st7712/nexo/hardware/CAD/PSU holder.stl

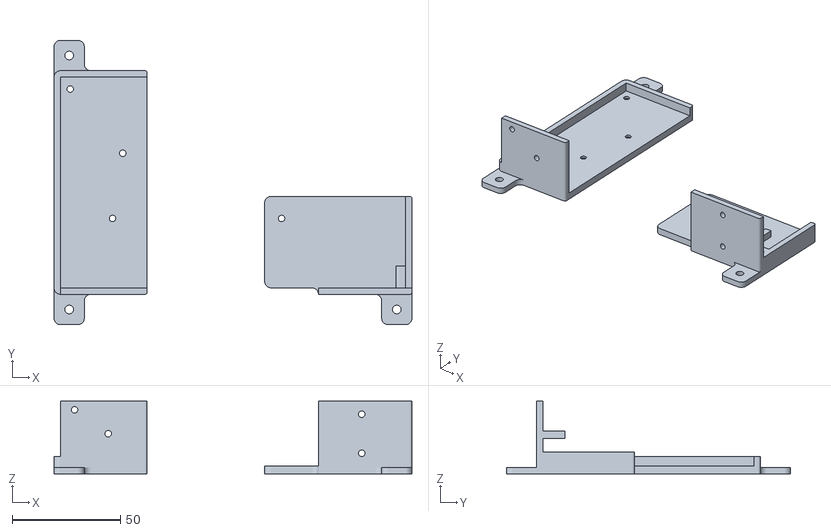
[picture p15: CAD file, 2026-02-17]
hardware/CAD/PSU holder.stl
165.2 x 131.2 x 33.5
