st7712/nexo/hardware/CAD/wood curve jig 1.stl

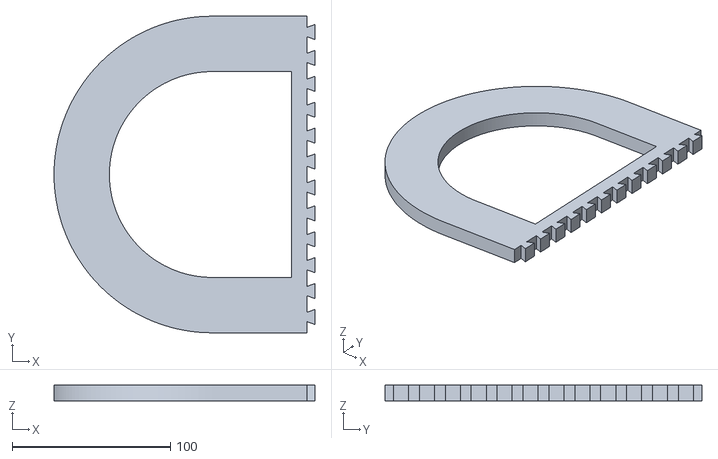
[picture p16: CAD file, 2026-02-17]
hardware/CAD/wood curve jig 1.stl
164.8 x 200.0 x 10.0
