st7712/nexo/hardware/CAD/speaker bottom rubber v3.stl

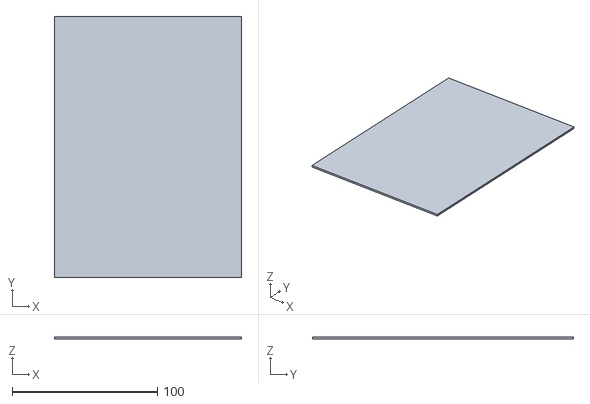
[picture p17: CAD file, 2026-02-17]
hardware/CAD/speaker bottom rubber v3.stl
129.0 x 180.0 x 1.50
