st7712/nexo/hardware/CAD/inside plaster enclosure 1.stl

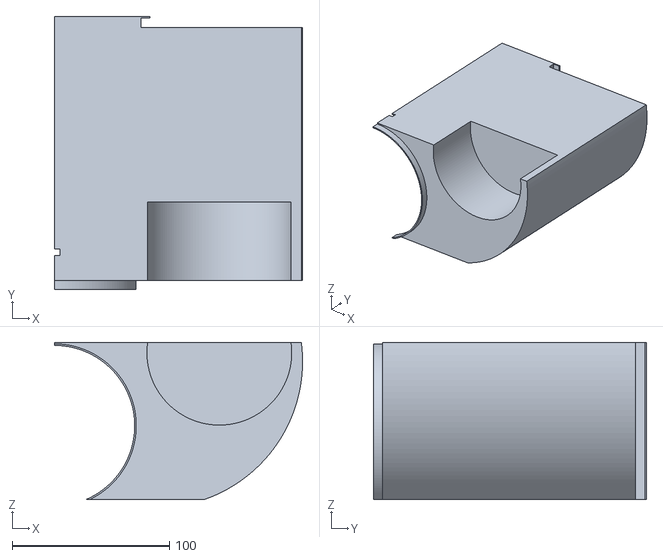
[picture p18: CAD file, 2026-02-17]
hardware/CAD/inside plaster enclosure 1.stl
158.0 x 173.8 x 100.2
