st7712/nexo/hardware/CAD/inside plaster enclosure 2.stl

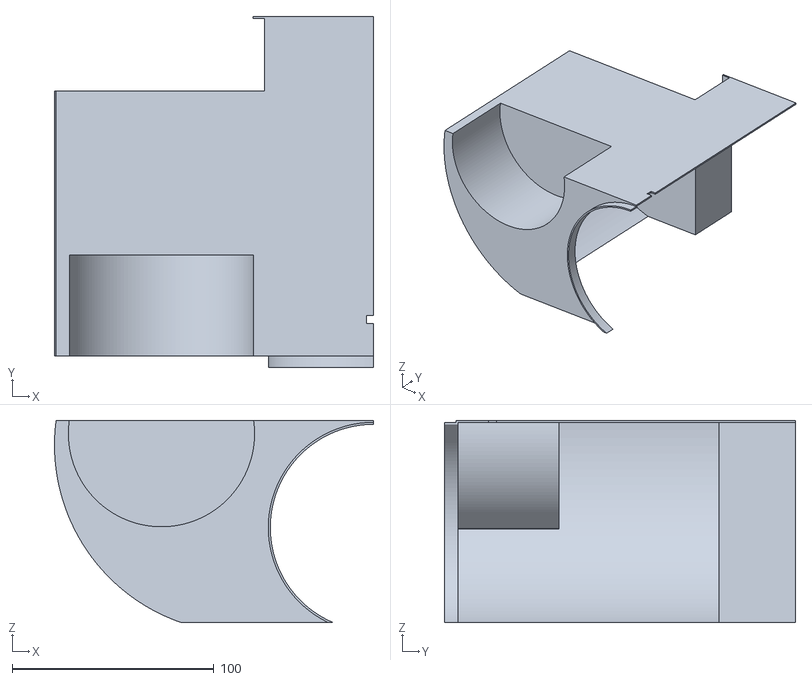
[picture p19: CAD file, 2026-02-17]
hardware/CAD/inside plaster enclosure 2.stl
158.0 x 173.8 x 100.2
