st7712/nexo/hardware/CAD/inside plaster enclosure top.stl

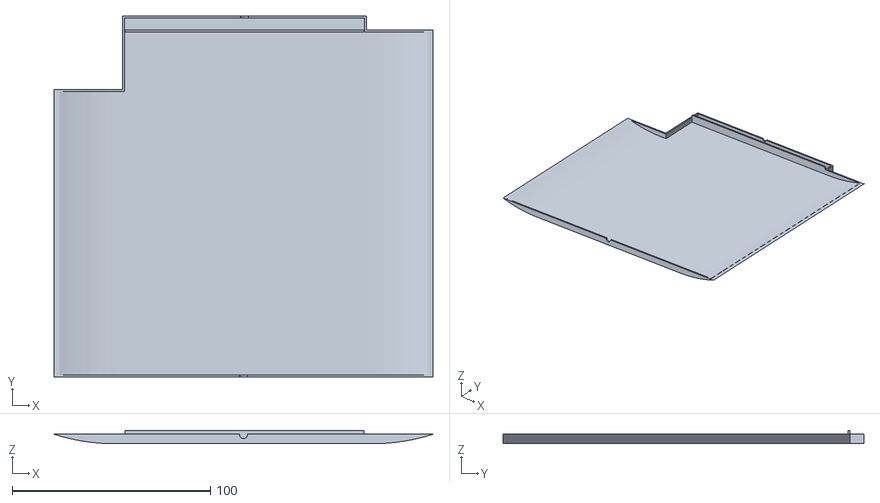
[picture p20: CAD file, 2026-02-17]
hardware/CAD/inside plaster enclosure top.stl
191.2 x 182.0 x 6.80
