st7712/nexo/hardware/CAD/front plate 1.stl

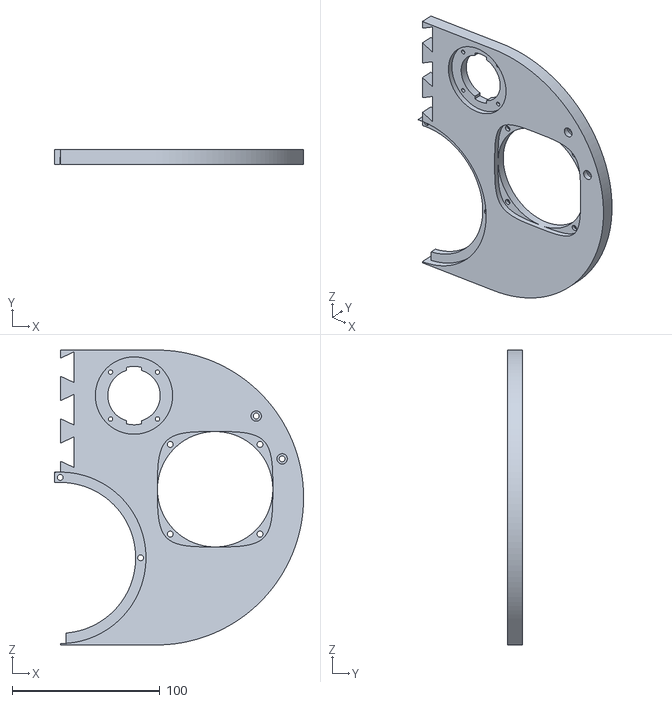
[picture p21: CAD file, 2026-02-17]
hardware/CAD/front plate 1.stl
169.0 x 10.0 x 200.0
