st7712/nexo/hardware/CAD/back plate 1.stl

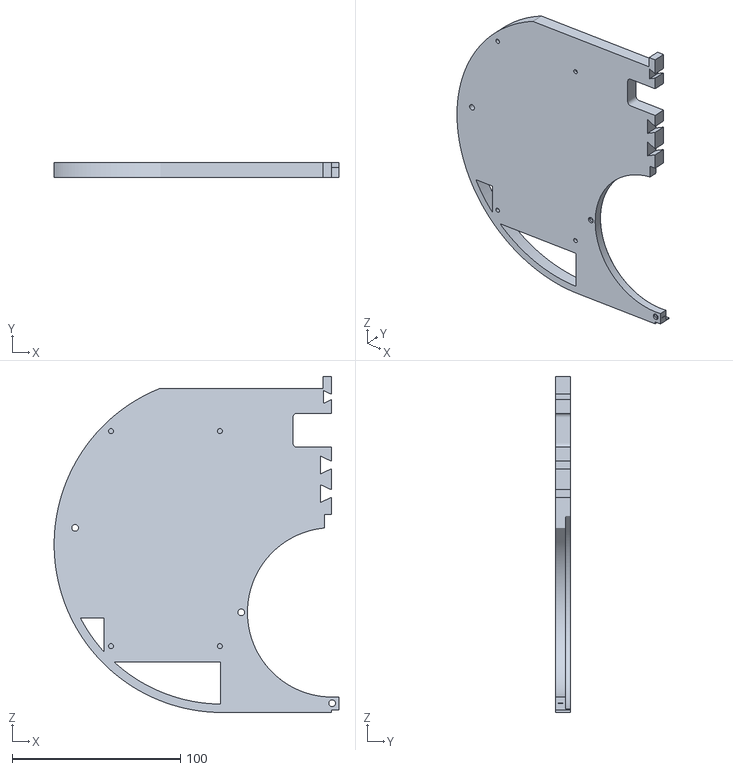
[picture p22: CAD file, 2026-02-17]
hardware/CAD/back plate 1.stl
169.5 x 9.00 x 200.0
